OrsoEric/gridfinity-bin-holder-openscad/images/2025-07-24_20_56_IMG_20250724_205657.jpg

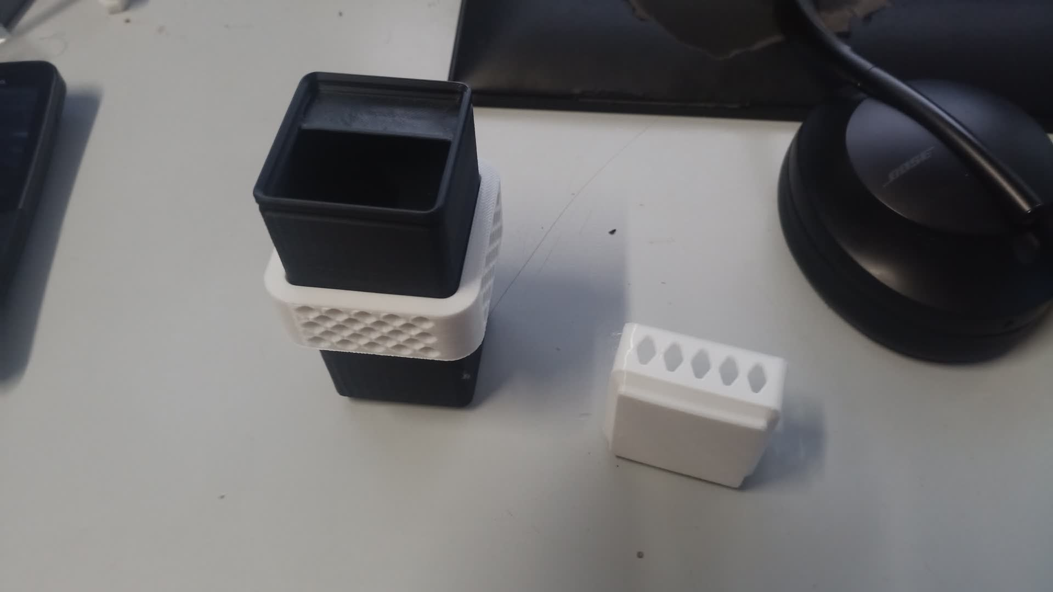
images/2025-07-24_20_56_IMG_20250724_205657.jpg
