OrsoEric/gridfinity-bin-holder-openscad/images/2025-07-24_20_57_IMG_20250724_205716.jpg

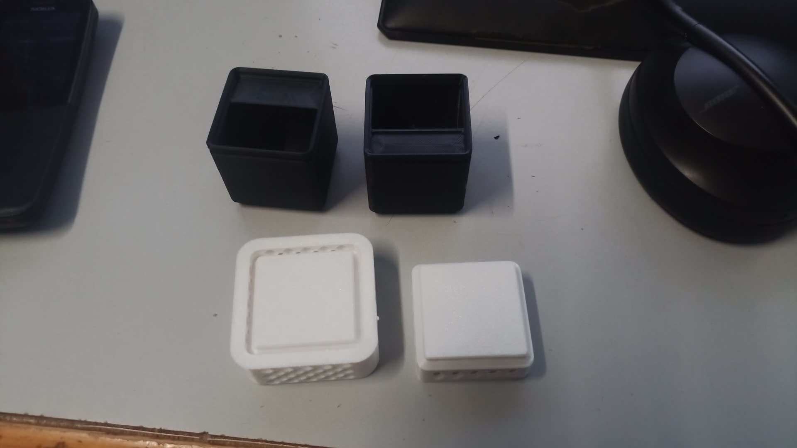
images/2025-07-24_20_57_IMG_20250724_205716.jpg
