OrsoEric/gridfinity-bin-holder-openscad/images/2025-07-24_20_58_IMG_20250724_205830.jpg

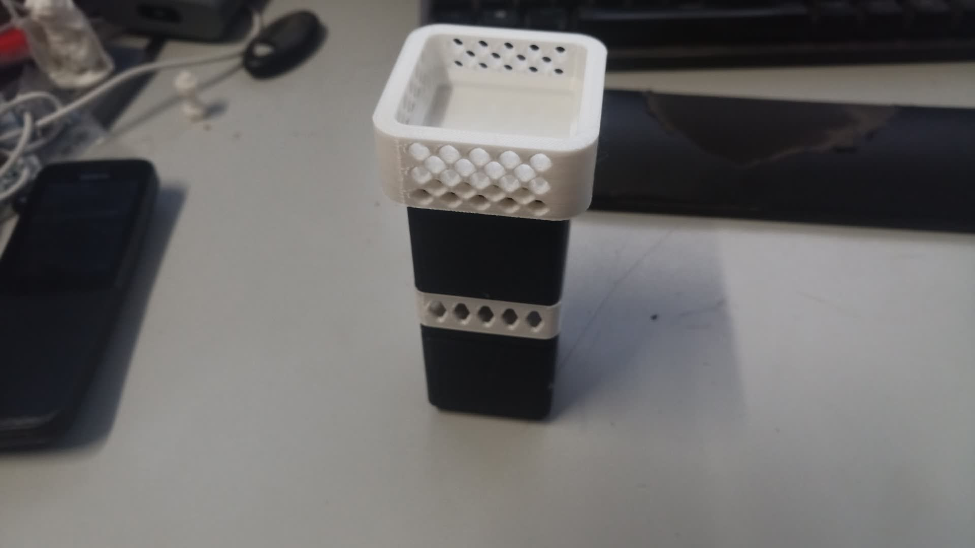
images/2025-07-24_20_58_IMG_20250724_205830.jpg
