OrsoEric/gridfinity-bin-holder-openscad/images/Rounded Diamond Sliced In Z HULL.jpg

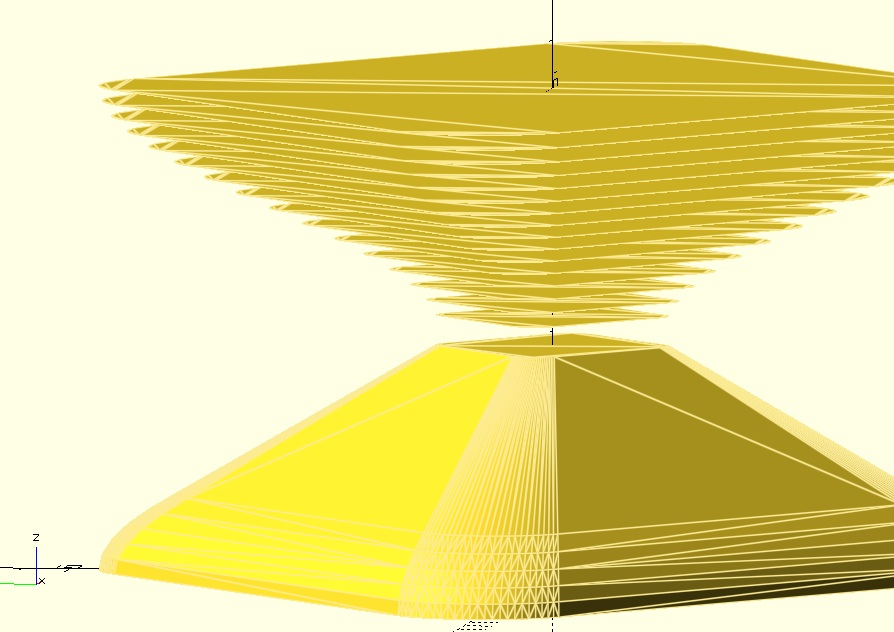
images/Rounded Diamond Sliced In Z HULL.jpg
