OrsoEric/gridfinity-bin-holder-openscad/images/Rounded Diamond Sliced In Z linear extrusion scale.jpg

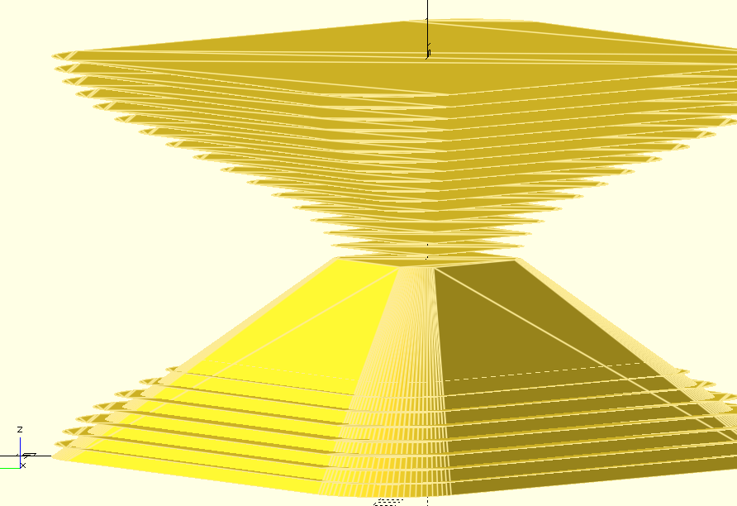
images/Rounded Diamond Sliced In Z linear extrusion scale.jpg
