OrsoEric/gridfinity-bin-holder-openscad/images/Screenshot 2025-07-27 114057.png

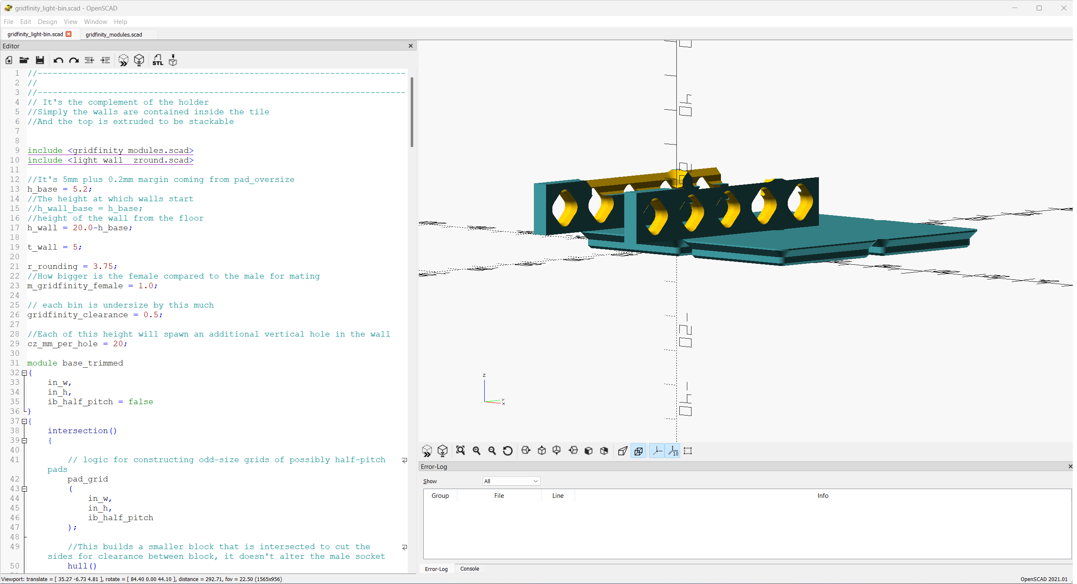
images/Screenshot 2025-07-27 114057.png
