OrsoEric/gridfinity-bin-holder-openscad/images/Screenshot 2025-07-27 124956.png

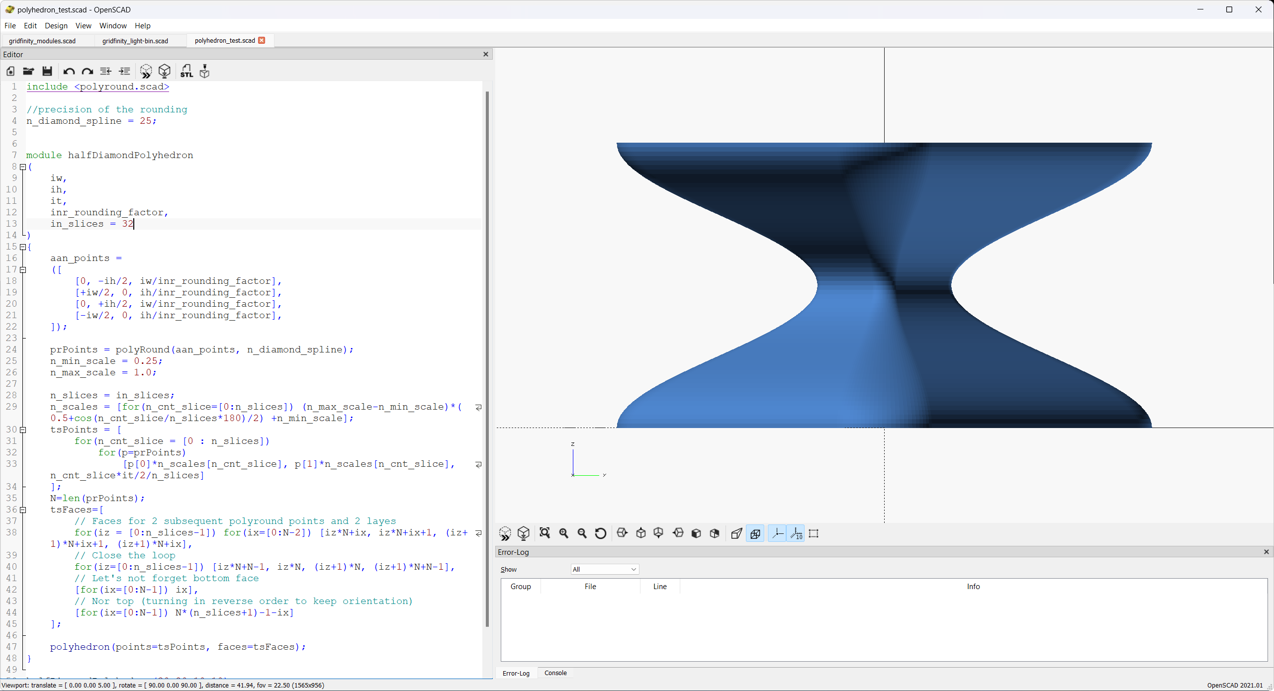
images/Screenshot 2025-07-27 124956.png
