OrsoEric/gridfinity-bin-holder-openscad/images/Screenshot 2025-07-27 125517.png

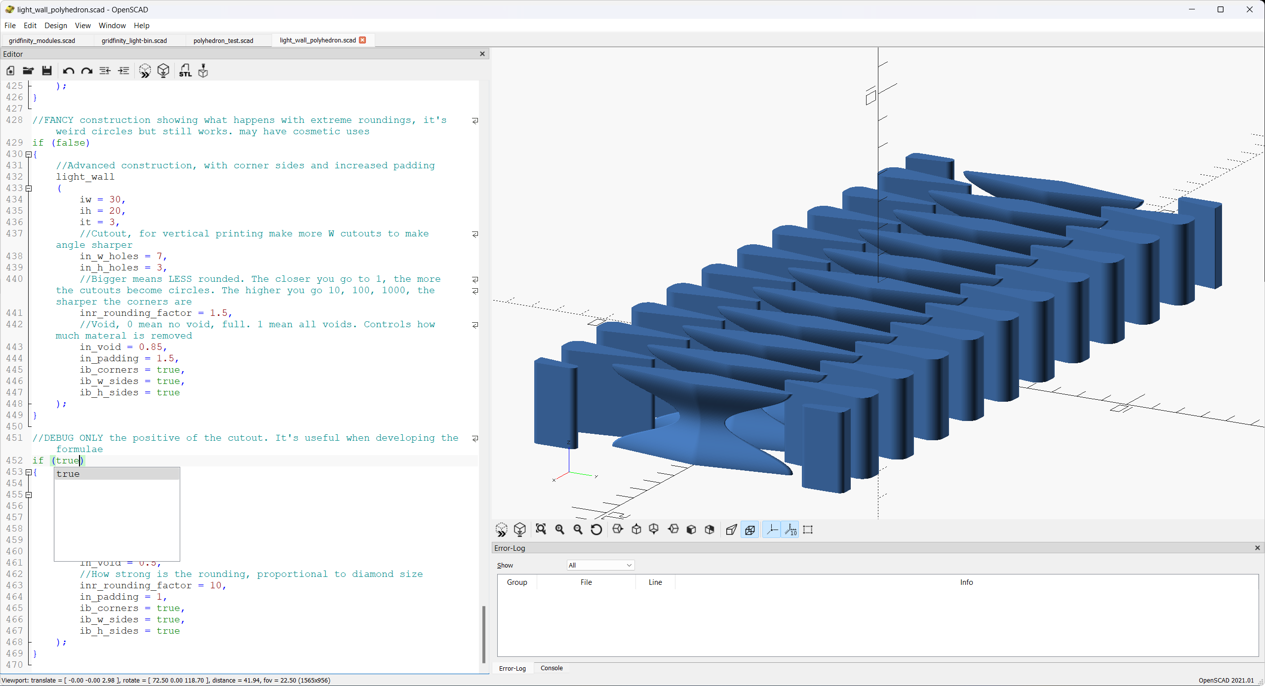
images/Screenshot 2025-07-27 125517.png
