OrsoEric/gridfinity-bin-holder-openscad/images/Screenshot 2025-07-27 134043.png

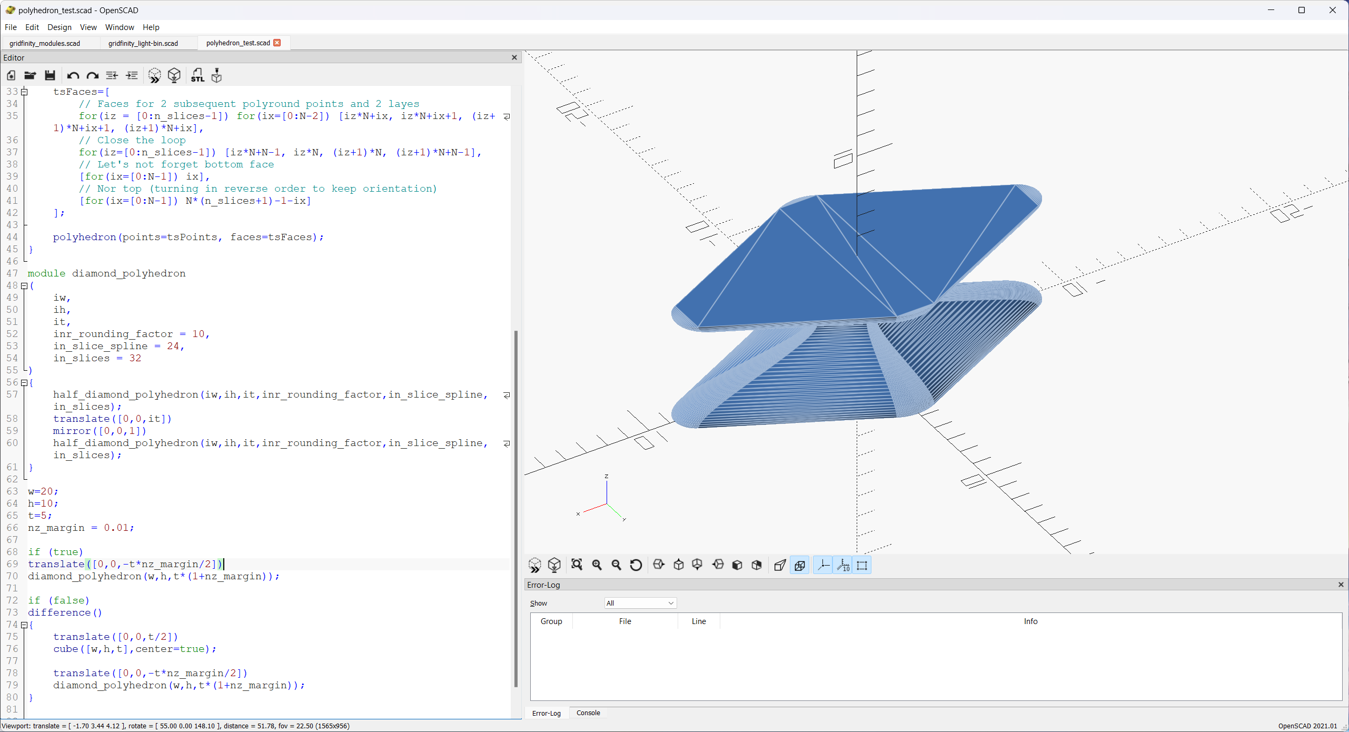
images/Screenshot 2025-07-27 134043.png
