OrsoEric/gridfinity-bin-holder-openscad/images/Screenshot 2025-07-28 110526.png

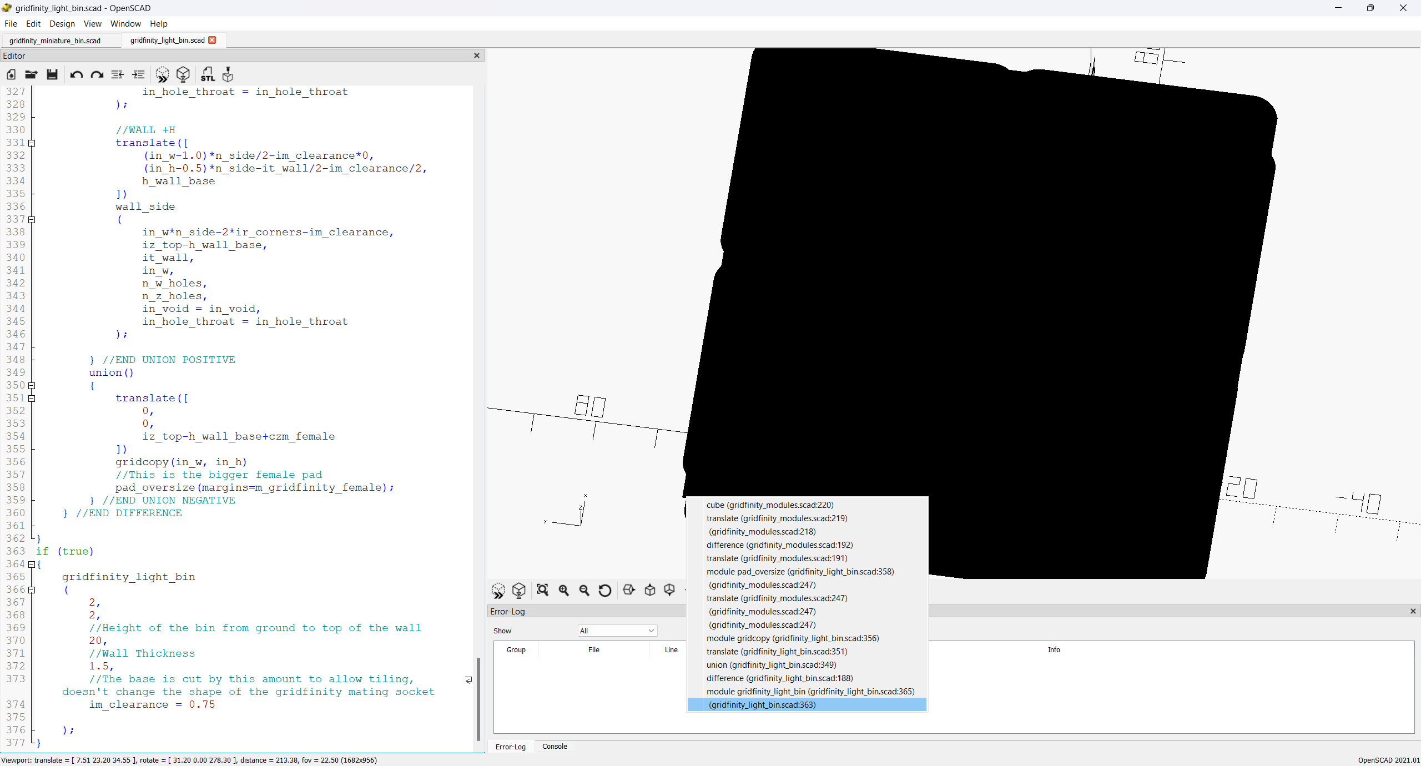
images/Screenshot 2025-07-28 110526.png
