OrsoEric/gridfinity-bin-holder-openscad/images/Screenshot (27).png

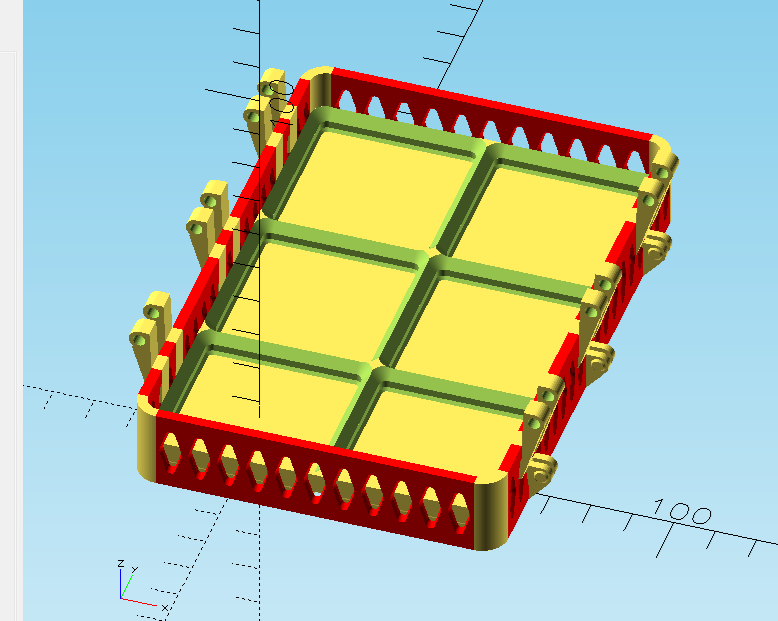
images/Screenshot (27).png
