OrsoEric/gridfinity-bin-holder-openscad/images/Screenshot (29).png

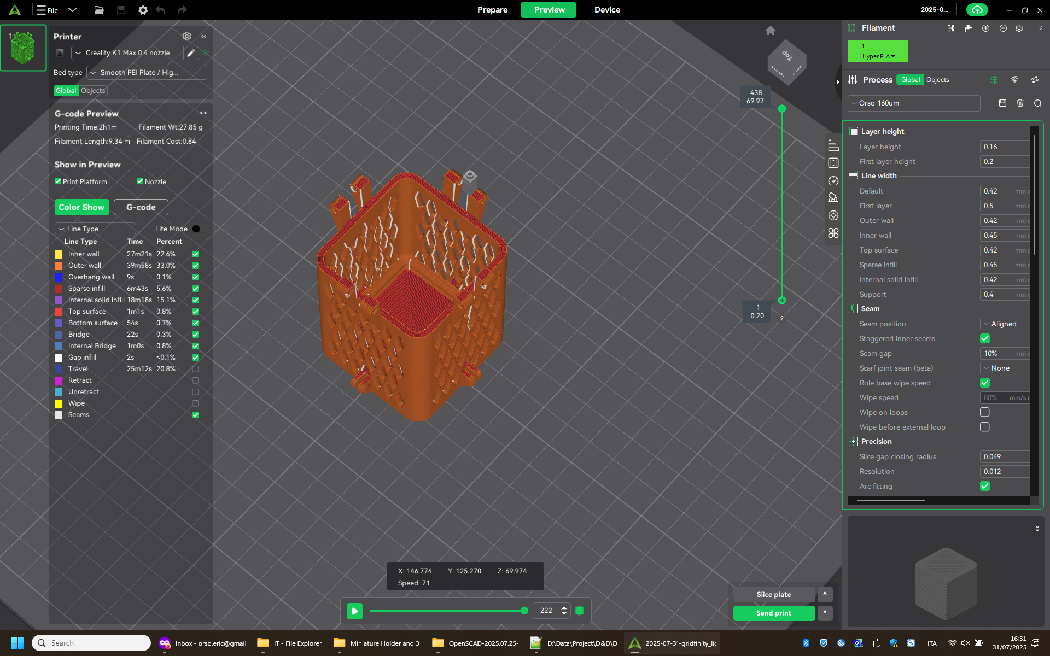
images/Screenshot (29).png
